tebl/8BIT-Wave/documentation/datasheets/PJ-210.jpg

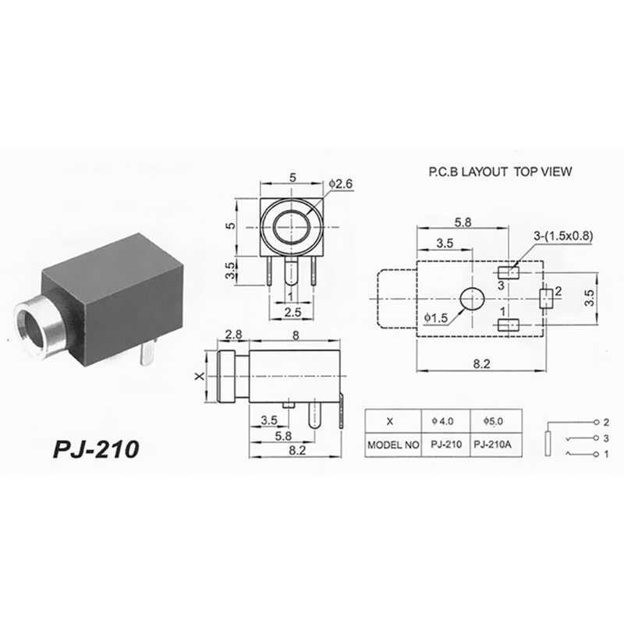
documentation/datasheets/PJ-210.jpg
