tebl/8BIT-Wave/gallery/8bitWave Faceplate.png

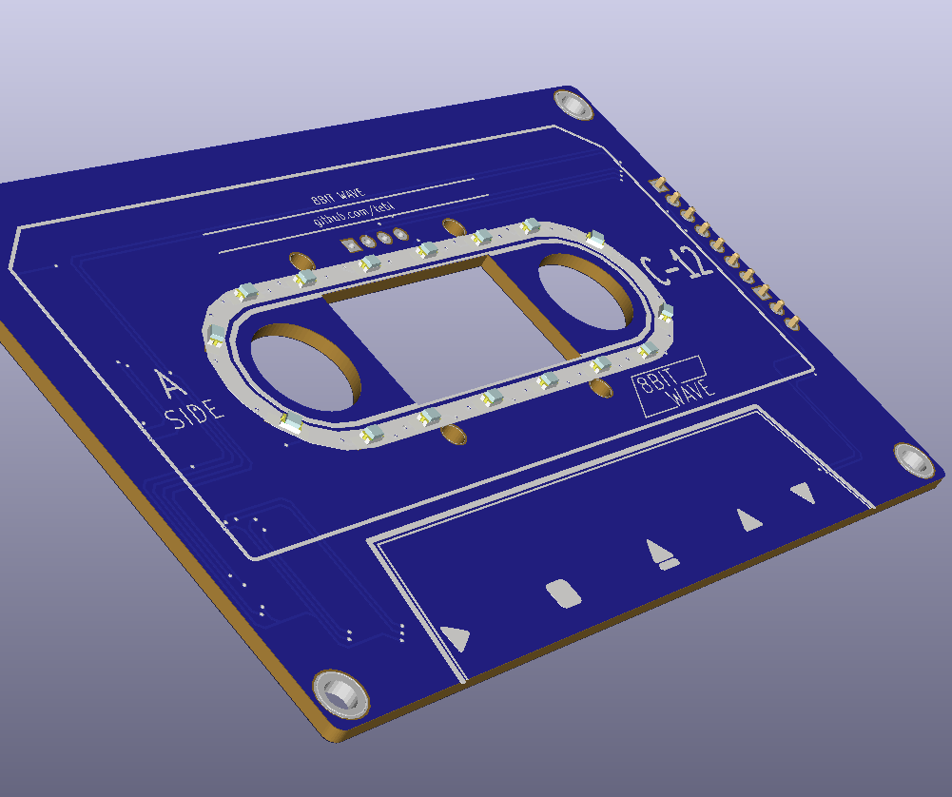
gallery/8bitWave Faceplate.png
