tebl/8BIT-Wave/gallery/2020-02-21 23.19.30.jpg

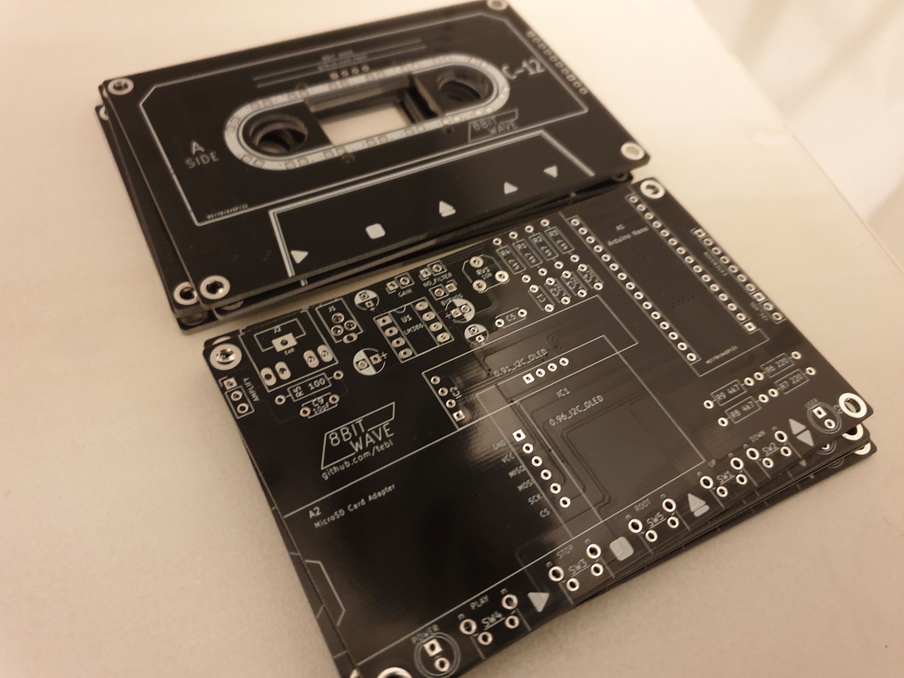
gallery/2020-02-21 23.19.30.jpg
