tebl/8BIT-Wave/gallery/2020-02-25 00.56.09.jpg

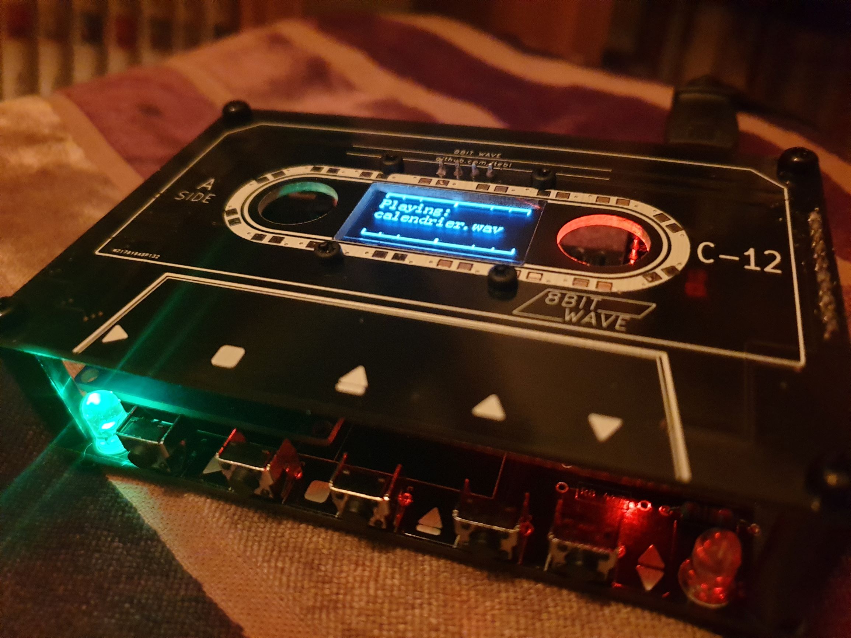
gallery/2020-02-25 00.56.09.jpg
