tebl/8BIT-Wave/gallery/2020-06-22 22.24.48.jpg

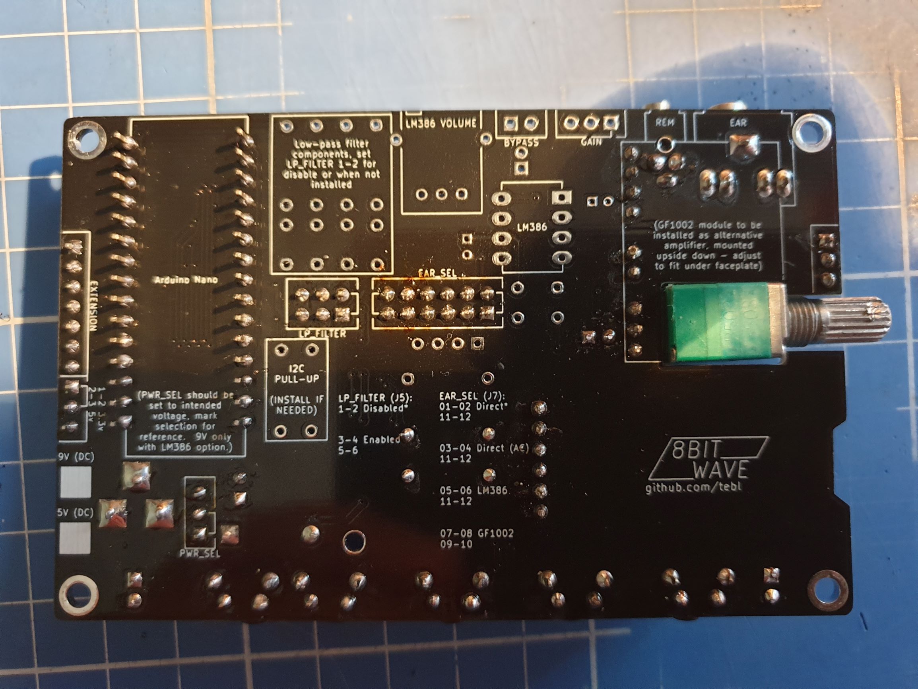
gallery/2020-06-22 22.24.48.jpg
