tebl/8BIT-Wave/software/arduino/8bit Wave/8bit-wave/led_control.h

void initialize_led();
void led_tick();
int get_led_mode(int pin_number);
void set_led_mode(int pin_number, int led_mode = LED_MODE_NONE);
void set_led_neutral(int pin_number);
void set_led_flash(int pin_number, int value = -1);
void set_led_cycle(int pin_number);
void set_led_fade_out(int pin_number, int value = -1, int tick_delay = 0);
int second_to_ticks(int num_seconds);
void flash_led_now(int pin_number, int num_flashes);
