tebl/8BIT-Wave/software/arduino/8bit Wave/8bit-wave/commands.cpp

#include <Arduino.h>
#include "constants.h"
#include "notice.h"
#include "display.h"
#include "led_control.h"
#include "process_sd.h"
#include "process_switches.h"
#include "process_rem.h"
#include "scrolling.h"
#include "player.h"
#include "commands.h"

char filename[FILENAME_MAX_LENGTH];
bool is_stopped = true;

#ifdef PLAYER_WAV
/*
 * Update volume setting as provided by the player - note that as the player
 * controls the volume, we can only tell it we want it to change and then
 * report the percentage we got back it.
 */
void volume_changed(int new_setting) {
    char message[OLED_LINE_WIDTH];
    sprintf(message, "(Volume %d%c)", new_setting, '%');
    set_notice(message);

    /* Set volume on USER LED, have it fade out after a while */
    set_led_fade_out(
      LED_USER,
      map(new_setting, 0, 100, LED_USER_MIN, LED_USER_MAX),
      second_to_ticks(10)
    );
}
void increase_volume() { volume_changed(wav_volume_up()); }
void decrease_volume() { volume_changed(wav_volume_down()); }
#endif

#ifdef PLAYER_CAS
/*
 * Update volume setting as provided by the player - note that as the player
 * controls the volume, we can only tell it we want it to change and then
 * report the percentage we got back it.
 */
void baud_rate_changed(int new_setting) {
  switch (new_setting) {
    default:
    case 1200: set_notice(F(TEXT_1200_BAUD)); break;
    case 2400: set_notice(F(TEXT_2400_BAUD)); break;
    case 3600: set_notice(F(TEXT_3600_BAUD)); break;  
  }

  /* Set volume on USER LED, have it fade out after a while */
  set_led_fade_out(
    LED_USER,
    map(new_setting, 1200, 3600, LED_USER_MIN, LED_USER_MAX),
    second_to_ticks(10)
  );
}
void baud_rate_up() { baud_rate_changed(cas_baud_rate_up()); }
void baud_rate_down() { baud_rate_changed(cas_baud_rate_down()); }
#endif

/*
 * Pressed up 
 */
void press_up() {
  if (!player_is_started()) {
    previous_file();
  }
}

/*
 * Pressed down
 */
void press_down() {
  if (!player_is_started()) {
    next_file();
  }
}

/*
 * Handle pause/resume.
 */
void press_pause() {
  if (!player_is_started() || is_stopped) return;

  if (player_is_paused()) {
    if (player_resume()) {
      display_set(OLED_LINE_0, F(TEXT_PLAYING));
      display_filename(OLED_LINE_1, filename);
      set_led_cycle(LED_POWER);
      set_timer_resume();
    }
  } else {
    if (player_pause()) {
      display_set(OLED_LINE_0, F(TEXT_PAUSED));
      set_led_flash(LED_POWER);
      set_timer_pause();
    }
  }
}

/*
 * Press the play button, this will have one of three different results based
 * on the circumstances; play a file if idle, pause a file if started or
 * resume if previously paused.
 */
void press_play() {
  if (is_stopped) {
    if (is_file_selected()) {
      set_notice(F(ERROR_FILE_NOT_FOUND));
    } else {
      player_start(filename);
      if (player_is_started()) {
        // Code only works if this println is here?
        Serial.println("is_started");
        configure_switches(PLAYER_RUNNING);
        is_stopped = false;

        display_set(OLED_LINE_0, F(TEXT_PLAYING));
        display_filename(OLED_LINE_1, filename);
        set_led_cycle(LED_POWER);
        set_timer_start();
      }
    }
  } else {
    press_pause();
  }
}

/*
 * Stop the player from making any more controlled noise. This function will
 * be called either when the stop button has been pushed, or when we detect
 * that the player has stopped in the background without us knowing about it.
 */
void do_stop() {
  player_stop();

  if (!player_is_started()) {
    display_set(OLED_LINE_0, F(TEXT_PLAY));
    set_led_neutral(LED_POWER);
    set_timer_stop();

    scroll_reset();
    set_timer_stop();

    configure_switches(PLAYER_IDLE);
    is_stopped = true;
  }
}

/*
 * Pressed stop button.
 */
void press_stop() {
  do_stop();
}

/*
 * Run regularly to verify that audio is still playing, if it has stopped
 * then we pretend the stop button was pushed really hard.
 */
void check_audio_finished() {
  if (!is_stopped and !player_is_started()) {
    do_stop();
    set_notice(F(NOTICE_DONE));
  }
}

/*
 * Configure switches according to the specified player mode, this is so that
 * we give different LED feedback depending on whichever functions are
 * available.
 */
void configure_switches(int player_state) {
  switch(player_state) {
    case PLAYER_IDLE:
      set_switch_callback(SW_PLAY, press_play);
      set_switch_callback(SW_STOP);
      set_switch_callback(SW_EJECT, nullptr, toggle_motor_controls);

      #ifdef PLAYER_WAV
      set_switch_callback(SW_UP, press_up, increase_volume);
      set_switch_callback(SW_DOWN, press_down, decrease_volume);
      #endif
      #ifdef PLAYER_CAS
      set_switch_callback(SW_UP, press_up, baud_rate_up);
      set_switch_callback(SW_DOWN, press_down, baud_rate_down);
      #endif
      break;
    default:
      set_switch_callback(SW_PLAY, press_play);
      set_switch_callback(SW_STOP, press_stop);
      set_switch_callback(SW_EJECT, nullptr, toggle_motor_controls);
      
      #ifdef PLAYER_WAV
      set_switch_callback(SW_UP, increase_volume);
      set_switch_callback(SW_DOWN, decrease_volume);
      #else
      set_switch_callback(SW_UP, baud_rate_up);
      set_switch_callback(SW_DOWN, baud_rate_down);
      #endif
      break;
  }
}

void initialize_commands() {
  memset(filename, 0, sizeof(filename));
  display_set(OLED_LINE_0, F(TEXT_PLAY));
  set_notice(F(NOTICE_LOAD_SD));

  configure_switches(PLAYER_IDLE);
}
