tebl/8BIT-Wave/software/arduino/8bit Wave/8bit-wave/notice.h

void clear_notice();
void set_notice(const char *string);
void set_notice(const __FlashStringHelper *string);

void set_timer_start();
void set_timer_stop();
void set_timer_pause();
void set_timer_resume();
void update_timer();
